ic1414/esp_trans_v2/doc/img_hard_md/Snipaste_2024-06-12_13-05-10.png

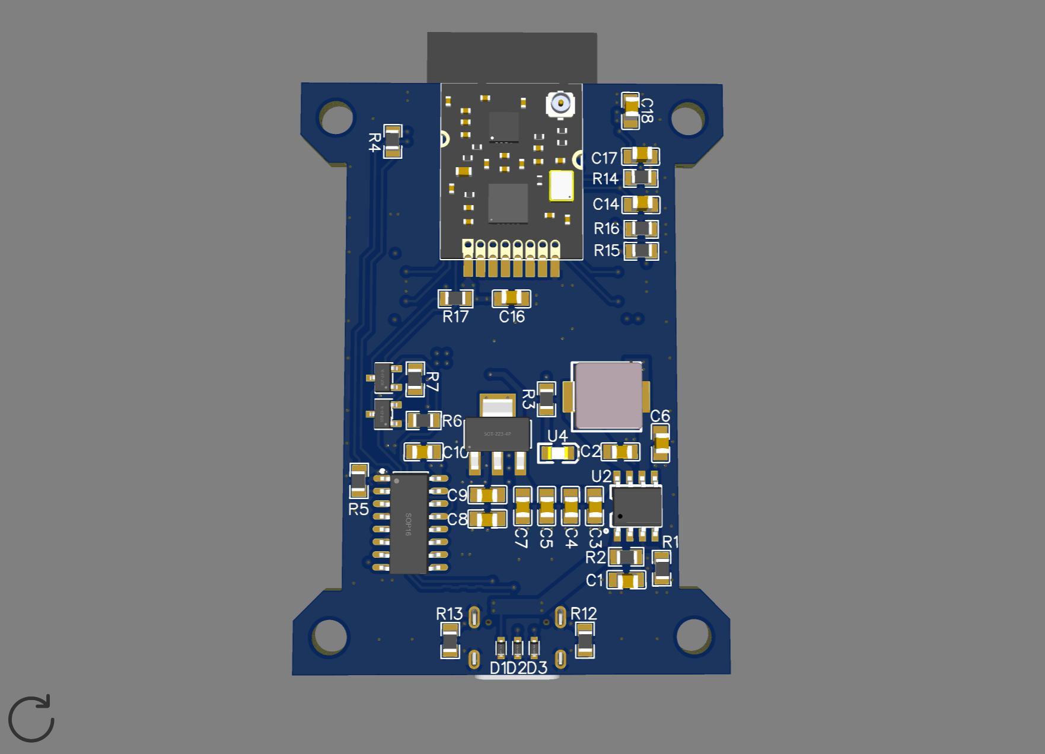
doc/img_hard_md/Snipaste_2024-06-12_13-05-10.png
